vroland/epdiy/src/output_lcd/lcd_driver.h

#pragma once

#include <driver/gpio.h>
#include <stdbool.h>
#include <stddef.h>
#include <stdint.h>
#ifndef __DECLARE_RCC_ATOMIC_ENV
#define __DECLARE_RCC_ATOMIC_ENV (0)
#endif
/**
 * LCD bus configuration parameters.
 */
typedef struct {
    // GPIO numbers of the parallel bus pins.
    gpio_num_t data[16];

    // horizontal clock pin.
    gpio_num_t clock;
    // vertical clock pin
    gpio_num_t ckv;

    // horizontal "Start Pulse", enabling data input on the line shift register
    gpio_num_t start_pulse;
    // latch enable
    gpio_num_t leh;
    // vertical start pulse, resetting the vertical line shift register.
    gpio_num_t stv;
} lcd_bus_config_t;

/// Configuration structure for the LCD-based Epd driver.
typedef struct {
    // high time for CKV in 1/10us.
    size_t pixel_clock;    // = 12000000
    int ckv_high_time;     // = 70
    int line_front_porch;  // = 4
    int le_high_time;      // = 4
    int bus_width;         // = 16
    lcd_bus_config_t bus;
} LcdEpdConfig_t;

typedef bool (*line_cb_func_t)(void*, uint8_t*);
typedef void (*frame_done_func_t)(void*);

void epd_lcd_init(const LcdEpdConfig_t* config, int display_width, int display_height);
void epd_lcd_deinit();
void epd_lcd_frame_done_cb(frame_done_func_t, void* payload);
void epd_lcd_line_source_cb(line_cb_func_t, void* payload);
void epd_lcd_start_frame();
/**
 * Set the LCD pixel clock frequency in MHz.
 */
void epd_lcd_set_pixel_clock_MHz(int frequency);
