vroland/epdiy/examples/weather/main/opensans8.h

#pragma once
#include "epdiy.h"
const uint8_t OpenSans8Bitmaps[69997] = {
    0x78, 0x9C, 0x03, 0x00, 0x00, 0x00, 0x00, 0x01, 0x78, 0x9C, 0xFB, 0xC9, 0xF8, 0x83, 0xE1, 0x3B,
    0xC3, 0x37, 0x86, 0x67, 0x0C, 0x57, 0x19, 0xAE, 0x30, 0x1C, 0x66, 0xD8, 0xCC, 0xA0, 0xC0, 0xF0,
    0x8B, 0xE9, 0x05, 0x23, 0x00, 0x89, 0x1A, 0x09, 0xEA, 0x78, 0x9C, 0x9B, 0x7B, 0x80, 0xAB, 0x67,
    0x03, 0x67, 0xD6, 0x04, 0x8E, 0xC8, 0x06, 0x36, 0x00, 0x22, 0x34, 0x04, 0x8E, 0x78, 0x9C, 0x63,
    0x60, 0xF0, 0x55, 0xE0, 0x67, 0x60, 0x60, 0xD0, 0x0F, 0xE0, 0x61, 0x60, 0x30, 0xE0, 0x6F, 0xE0,
    0x64, 0x60, 0x08, 0xE0, 0x59, 0xC0, 0xC6, 0xF0, 0xE0, 0x3F, 0x10, 0x70, 0x30, 0x1C, 0x60, 0xFB,
    0xC4, 0xC8, 0xC0, 0xF0, 0x81, 0x71, 0x1B, 0x03, 0xC3, 0x4F, 0x90, 0x08, 0x83, 0xC0, 0x0E, 0xC1,
    0x58, 0x41, 0x06, 0x86, 0x2A, 0x06, 0x7D, 0xA0, 0xA6, 0x58, 0x84, 0x56, 0x00, 0xBD, 0x43, 0x13,
    0x12, 0x78, 0x9C, 0x63, 0xD8, 0xC0, 0xC6, 0xC0, 0x00, 0xC4, 0x09, 0x7F, 0xDF, 0x4B, 0x7D, 0xDB,
    0xE6, 0xCE, 0xB1, 0x1B, 0xC8, 0x7E, 0xB1, 0x99, 0x8D, 0x61, 0xC3, 0x7F, 0x2D, 0x06, 0x86, 0xCB,
    0xFF, 0x39, 0x19, 0x36, 0x84, 0xE5, 0x03, 0xE5, 0x7B, 0x33, 0x37, 0xCF, 0xB4, 0xBF, 0xF1, 0x7F,
    0x1D, 0x33, 0x03, 0x54, 0x3D, 0x00, 0x65, 0xDD, 0x15, 0x34, 0x78, 0x9C, 0x33, 0x78, 0xCB, 0xC9,
    0xD0, 0xC0, 0xCD, 0x70, 0x40, 0x3C, 0x87, 0xE1, 0x23, 0x13, 0xC3, 0x07, 0xC6, 0x6D, 0x0C, 0xB3,
    0x18, 0x18, 0x3E, 0x32, 0x1C, 0x35, 0x90, 0x63, 0x00, 0xF1, 0x0E, 0xB0, 0x33, 0x80, 0xE4, 0xAE,
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
    {0x2190, 0x21FF, 0x10F}, {0x2300, 0x23FF, 0x17F}, {0x25A0, 0x25FF, 0x27F},
    {0x2600, 0x26F0, 0x2DF}, {0x2700, 0x27BF, 0x3D0},
};
const EpdFont OpenSans8 = {
    OpenSans8Bitmaps, OpenSans8Glyphs, OpenSans8Intervals, 8, 1, 23, 18, -5,
};
