vroland/epdiy/examples/http-server/main/server.h

#ifndef SERVER_H
#define SERVER_H

#include <stdio.h>
#include <string.h>
#include "freertos/FreeRTOS.h"
#include "freertos/task.h"
#include "esp_event.h"
#include "esp_log.h"
#include "nvs_flash.h"
#include "esp_wifi.h"
#include "esp_netif.h"
#include "esp_http_server.h"

#include "settings.h"

httpd_handle_t get_server(void);

#endif /* SERVER_H */
