vroland/epdiy/examples/http-server/main/settings.h

#ifndef SETTINGS_H
#define SETTINGS_H

#define WIFI_SSID "best ssid"                    // Replace with your Wi-Fi SSID
#define WIFI_PASSWORD "great password much wow"  // Replace with your Wi-Fi password

#define SCREEN_MODEL ED060XC3

#endif /* SETTINGS_H */
